sahilchess/Pokemon-Hackpad/assets/icon-progress-rounded.dxf

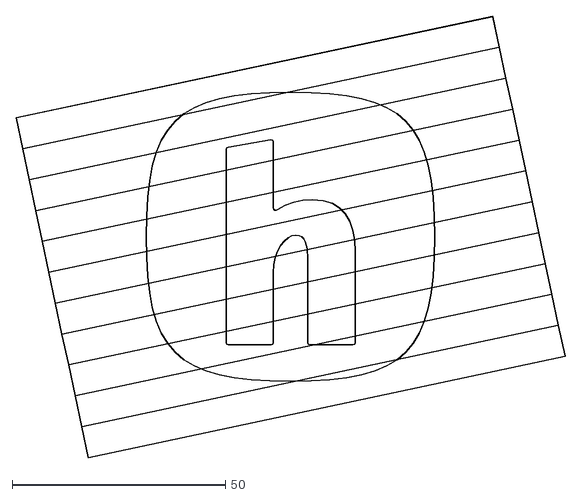
[picture p17: CAD file, 2026-07-08]
assets/icon-progress-rounded.dxf
128.9 x 103.5
