sahilchess/Pokemon-Hackpad/assets/graphics1.dxf

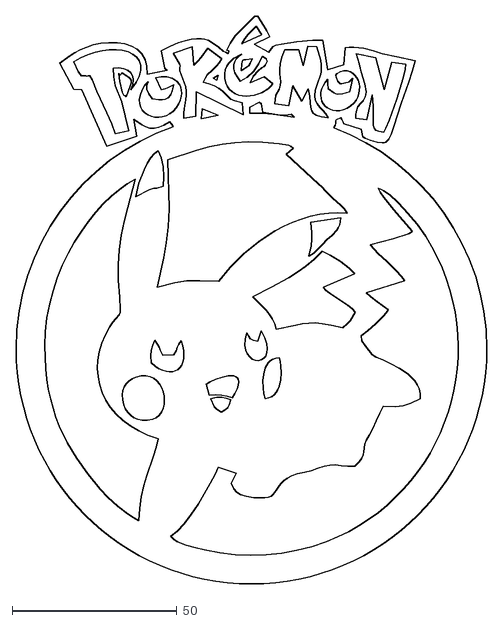
[picture p18: CAD file, 2026-07-08]
assets/graphics1.dxf
142.6 x 172.1
