sahilchess/Pokemon-Hackpad/assets/plate.dxf

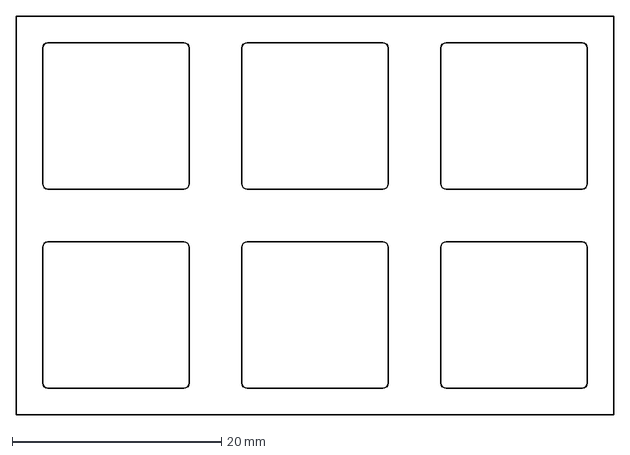
[picture p19: CAD file, 2026-07-08]
assets/plate.dxf
57.1 x 38.1 mm
